targetdisk/td-ez/hw/revA/revA.kicad_sch

## KiCad design hw/revA/revA.kicad_sch (2023-12-05, an earlier design)

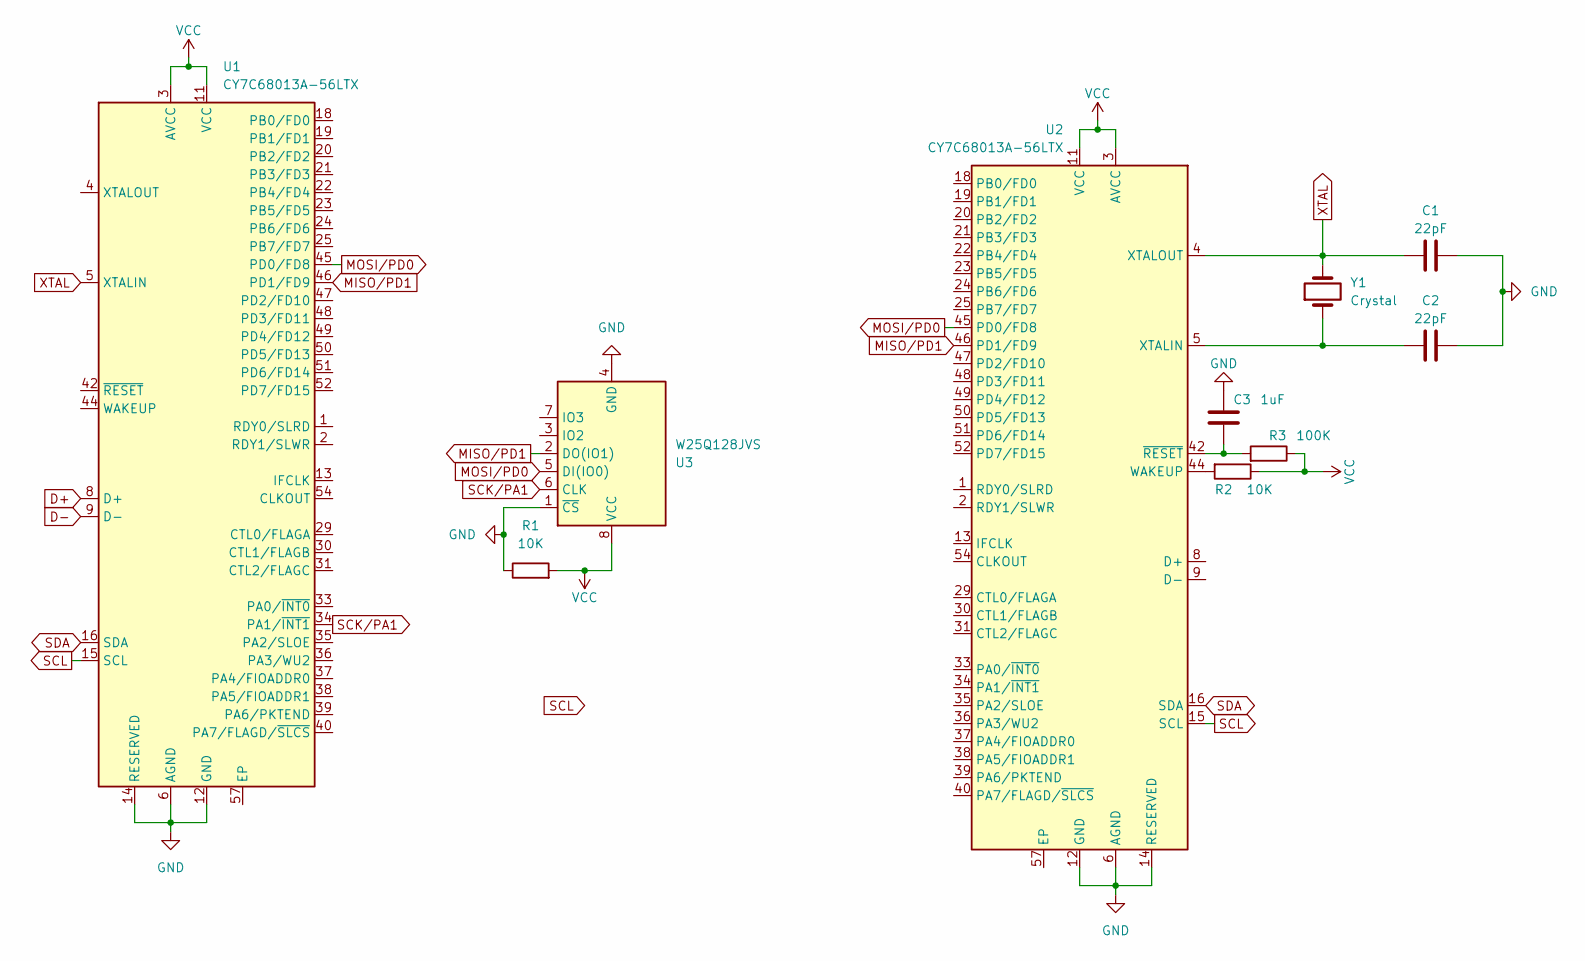
[picture p2: schematic revA.kicad_sch]

Parts:
C1, C2: 22pF
C3: 1uF
R1, R2: 10K
R3: 100K
U1, U2: CY7C68013A-56LTX; QFN-56-1EP_8x8mm_P0.5mm_EP4.5x5.2mm_ThermalVias_TopTented
U3: W25Q128JVS; WSON-8-1EP_6x5mm_P1.27mm_EP3.4x4mm
Y1: Crystal

Connections:
D+: U1.8 (D+)
D-: U1.9 (D-)
GND: C1.1, C2.1, C3.1, R1.1, U1.6 (AGND), U1.10 (AGND), U1.12 (GND), U1.14 (RESERVED), U1.26 (GND), U1.28 (GND), U1.41 (GND), U1.53 (GND), U1.56 (GND), U2.6 (AGND), U2.10 (AGND), U2.12 (GND), U2.14 (RESERVED), U2.26 (GND), U2.28 (GND), U2.41 (GND), U2.53 (GND), U2.56 (GND), U3.1 (~CS), U3.4 (GND)
MISO/PD1: U1.46 (PD1/FD9), U2.46 (PD1/FD9), U3.2 (DO(IO1))
MOSI/PD0: U1.45 (PD0/FD8), U2.45 (PD0/FD8), U3.5 (DI(IO0))
unnamed: C2.2, U2.5 (XTALIN), Y1.1
unnamed: C3.2, R3.2, U2.42 (~RESET)
unnamed: R2.2, U2.44 (WAKEUP)
SCK/PA1: U1.34 (PA1/~INT1), U3.6 (CLK)
SCL: U1.15 (SCL), U2.15 (SCL)
SDA: U1.16 (SDA), U2.16 (SDA)
VCC: R1.2, R2.1, R3.1, U1.3 (AVCC), U1.7 (AVCC), U1.11 (VCC), U1.17 (VCC), U1.27 (VCC), U1.32 (VCC), U1.43 (VCC), U1.55 (VCC), U2.3 (AVCC), U2.7 (AVCC), U2.11 (VCC), U2.17 (VCC), U2.27 (VCC), U2.32 (VCC), U2.43 (VCC), U2.55 (VCC), U3.8 (VCC)
XTAL: C1.2, U1.5 (XTALIN), U2.4 (XTALOUT), Y1.2
